Sonicators/UltrasonicSystem/Hardware/45mm/ParabolicHorn/ReactionChamber/Front.dxf

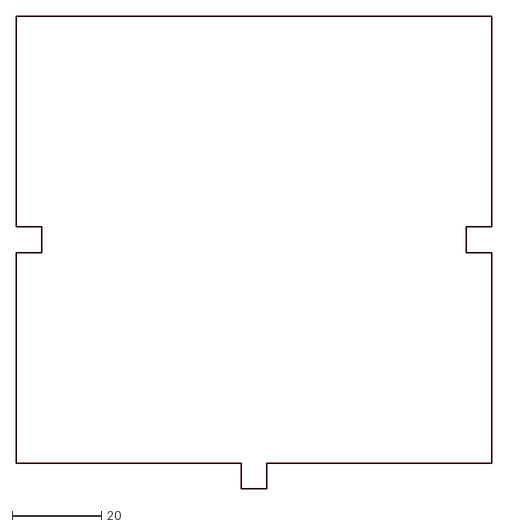
[picture p15: CAD file, 2015-09-21]
Hardware/45mm/ParabolicHorn/ReactionChamber/Front.dxf
106.4 x 105.7
