Sonicators/UltrasonicSystem/Hardware/45mm/StepHorn/DrillPressMount/UpperClamp.dxf

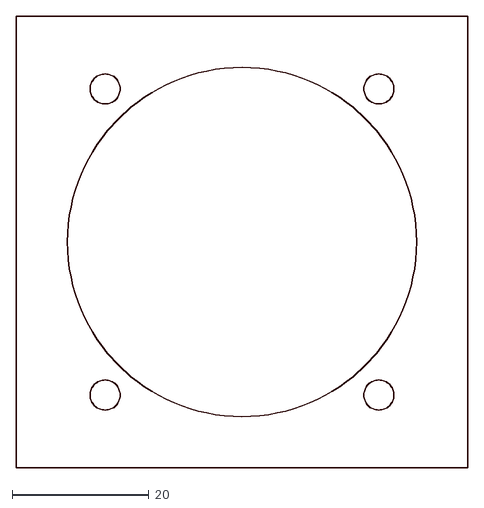
[picture p16: CAD file, 2015-09-21]
Hardware/45mm/StepHorn/DrillPressMount/UpperClamp.dxf
66.0 x 66.0
