Sonicators/UltrasonicSystem/Hardware/67mm/CameraMount/Ring.dxf

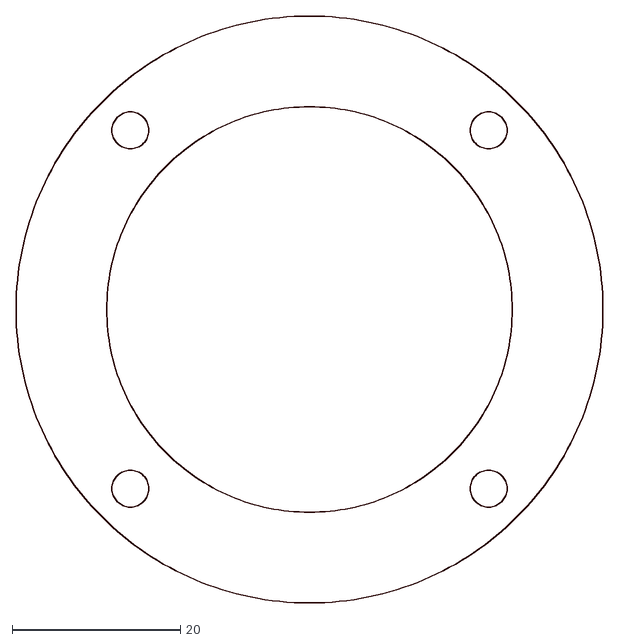
[picture p17: CAD file, 2015-09-21]
Hardware/67mm/CameraMount/Ring.dxf
69.8 x 69.8
