Sonicators/UltrasonicSystem/Hardware/67mm/Clamp/UpperClamp.dxf

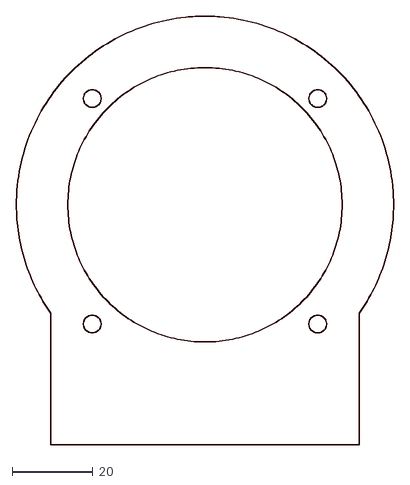
[picture p18: CAD file, 2015-09-21]
Hardware/67mm/Clamp/UpperClamp.dxf
93.6 x 106.4
