Sonicators/UltrasonicSystem/Hardware/45mm/CameraMount/LowerClamp.dxf

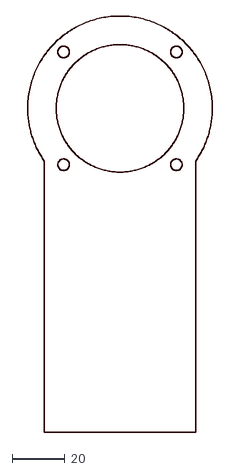
[picture p19: CAD file, 2015-09-21]
Hardware/45mm/CameraMount/LowerClamp.dxf
69.8 x 157.4
