Sonicators/UltrasonicSystem/Hardware/45mm/Clamp/LowerClamp.dxf

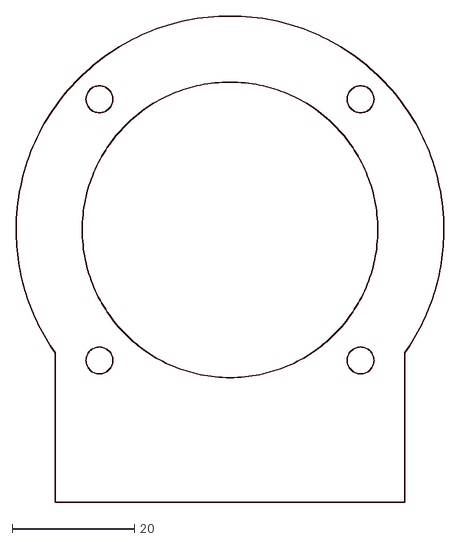
[picture p20: CAD file, 2015-09-21]
Hardware/45mm/Clamp/LowerClamp.dxf
69.8 x 79.4
