Sonicators/UltrasonicSystem/Hardware/45mm/DrillPressMount/UpperClamp.dxf

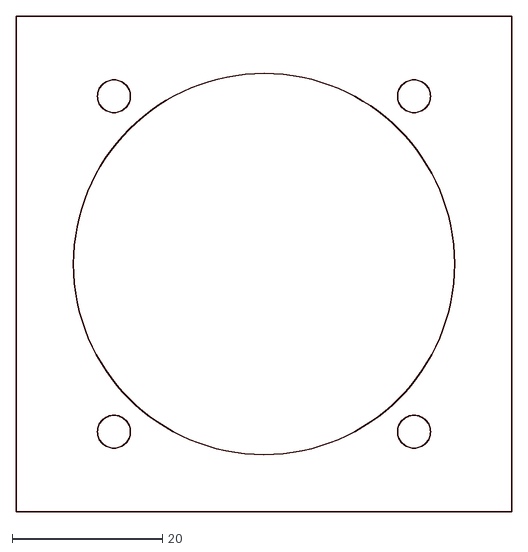
[picture p21: CAD file, 2015-09-21]
Hardware/45mm/DrillPressMount/UpperClamp.dxf
66.0 x 66.0
