Sonicators/UltrasonicSystem/Hardware/45mm/ParabolicHorn/ReactionChamber/Gasket.dxf

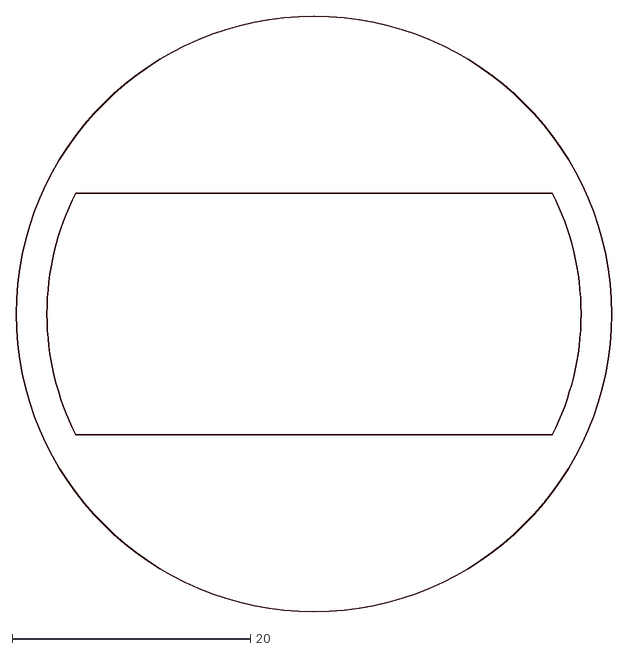
[picture p22: CAD file, 2015-09-21]
Hardware/45mm/ParabolicHorn/ReactionChamber/Gasket.dxf
50.0 x 50.0
