Sonicators/UltrasonicSystem/Hardware/67mm/CameraMount/UpperClamp.dxf

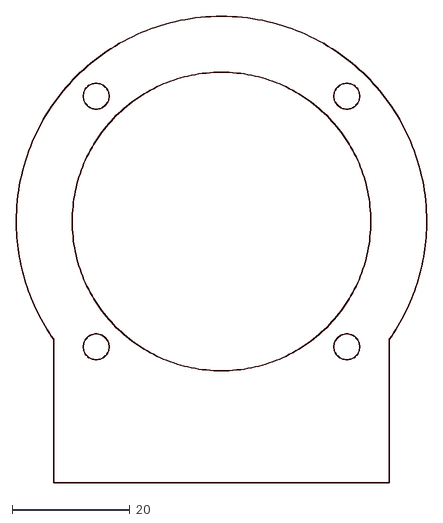
[picture p23: CAD file, 2015-09-21]
Hardware/67mm/CameraMount/UpperClamp.dxf
69.8 x 79.4
