Sonicators/UltrasonicSystem/Hardware/67mm/Clamp/LowerClamp.dxf

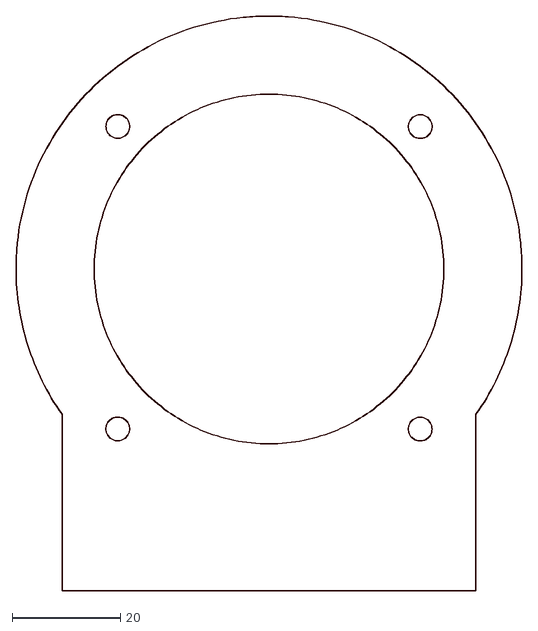
[picture p24: CAD file, 2015-09-21]
Hardware/67mm/Clamp/LowerClamp.dxf
93.6 x 106.4
