Sonicators/UltrasonicSystem/Hardware/45mm/CameraMount/Ring.dxf

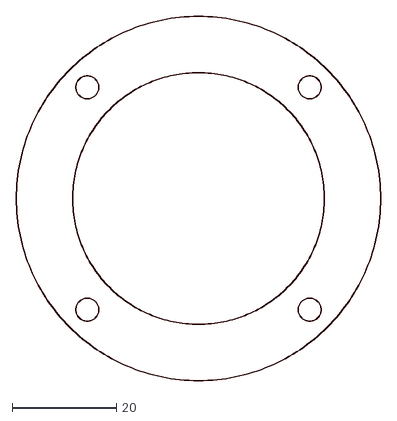
[picture p25: CAD file, 2015-09-21]
Hardware/45mm/CameraMount/Ring.dxf
69.8 x 69.8
