Sonicators/UltrasonicSystem/Hardware/45mm/ParabolicHorn/DrillPressMount/Gasket.dxf

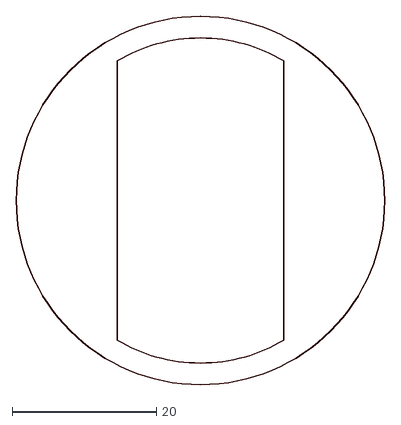
[picture p26: CAD file, 2015-09-21]
Hardware/45mm/ParabolicHorn/DrillPressMount/Gasket.dxf
51.0 x 51.0
