Sonicators/UltrasonicSystem/Hardware/45mm/ParabolicHorn/ReactionChamber/TubeHolder.dxf

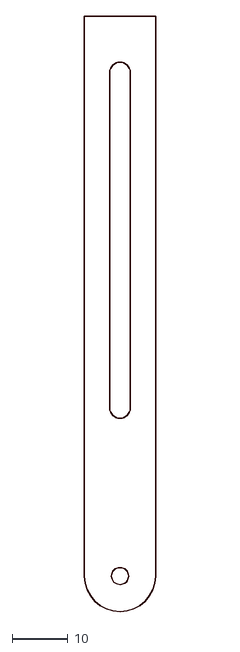
[picture p27: CAD file, 2015-09-21]
Hardware/45mm/ParabolicHorn/ReactionChamber/TubeHolder.dxf
12.7 x 106.3
