Sonicators/UltrasonicSystem/Hardware/67mm/CameraMount/BraceCorners.dxf

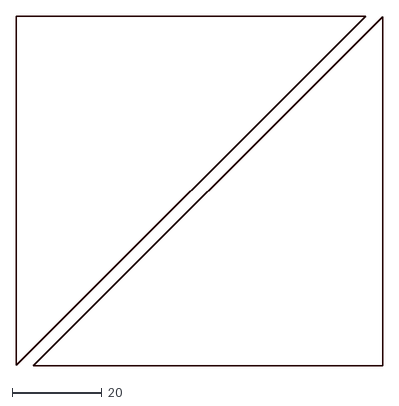
[picture p28: CAD file, 2015-09-21]
Hardware/67mm/CameraMount/BraceCorners.dxf
81.8 x 78.1
