Sonicators/UltrasonicSystem/Hardware/45mm/CameraMount/CameraBase.dxf

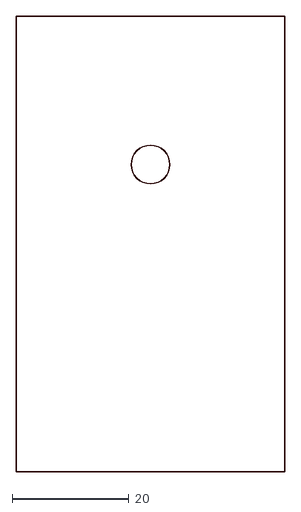
[picture p29: CAD file, 2015-09-21]
Hardware/45mm/CameraMount/CameraBase.dxf
46.0 x 78.0
