Sonicators/UltrasonicSystem/Hardware/45mm/ParabolicHorn/ReactionChamber/Side.dxf

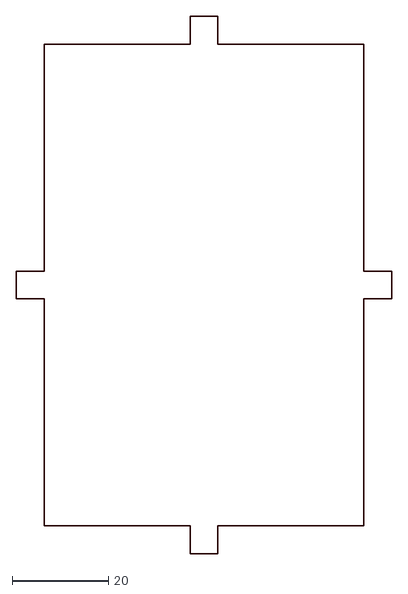
[picture p30: CAD file, 2015-09-21]
Hardware/45mm/ParabolicHorn/ReactionChamber/Side.dxf
77.8 x 111.5
