Sonicators/UltrasonicSystem/Hardware/67mm/CameraMount/Gasket.dxf

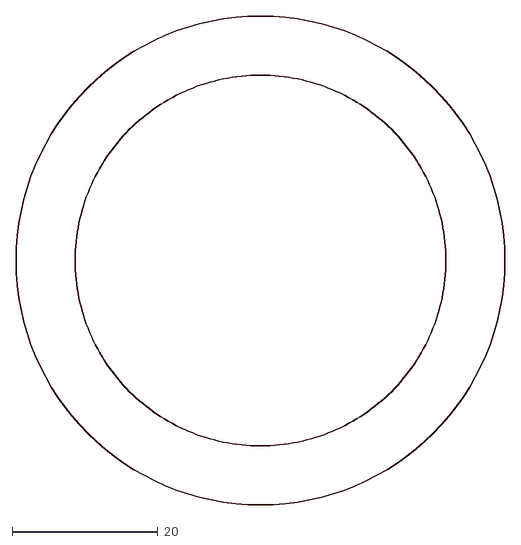
[picture p31: CAD file, 2015-09-21]
Hardware/67mm/CameraMount/Gasket.dxf
67.0 x 67.0
