Sonicators/UltrasonicSystem/Hardware/45mm/ParabolicHorn/ReactionChamber/TopRoundGasket.dxf

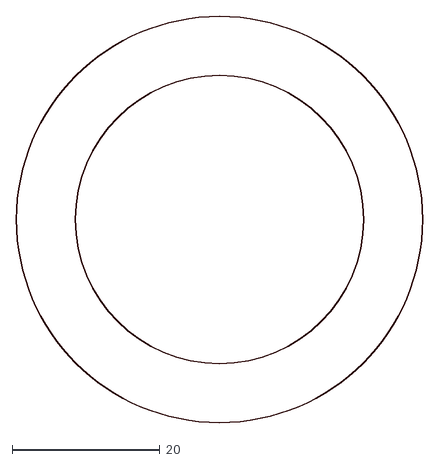
[picture p32: CAD file, 2015-09-21]
Hardware/45mm/ParabolicHorn/ReactionChamber/TopRoundGasket.dxf
55.0 x 55.0
