Sonicators/UltrasonicSystem/Hardware/67mm/CameraMount/LowerClamp.dxf

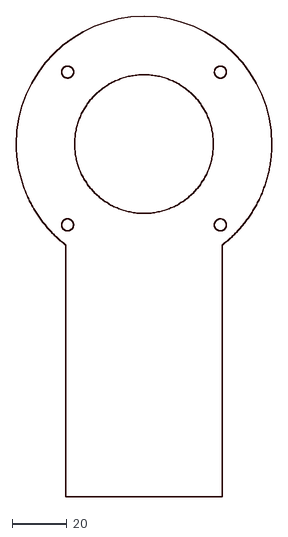
[picture p33: CAD file, 2015-09-21]
Hardware/67mm/CameraMount/LowerClamp.dxf
93.6 x 176.0
