Sonicators/UltrasonicSystem/Hardware/45mm/ParabolicHorn/ReactionChamber/TopRoundWide.dxf

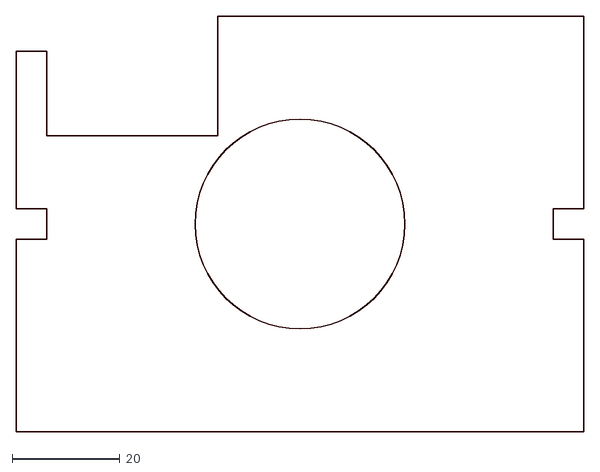
[picture p34: CAD file, 2015-09-21]
Hardware/45mm/ParabolicHorn/ReactionChamber/TopRoundWide.dxf
105.6 x 77.3
