Sonicators/UltrasonicSystem/Hardware/45mm/ParabolicHorn/ReactionChamber/Base.dxf

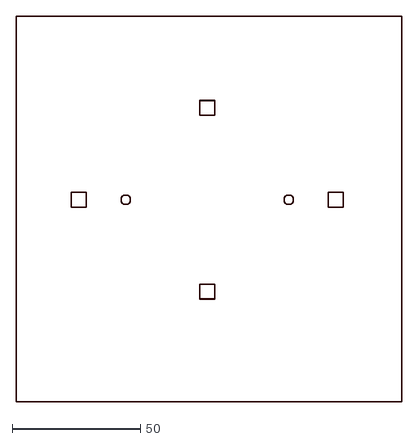
[picture p35: CAD file, 2015-09-21]
Hardware/45mm/ParabolicHorn/ReactionChamber/Base.dxf
150.0 x 150.0
