Sonicators/UltrasonicSystem/Hardware/45mm/ParabolicHorn/ReactionChamber/Back.dxf

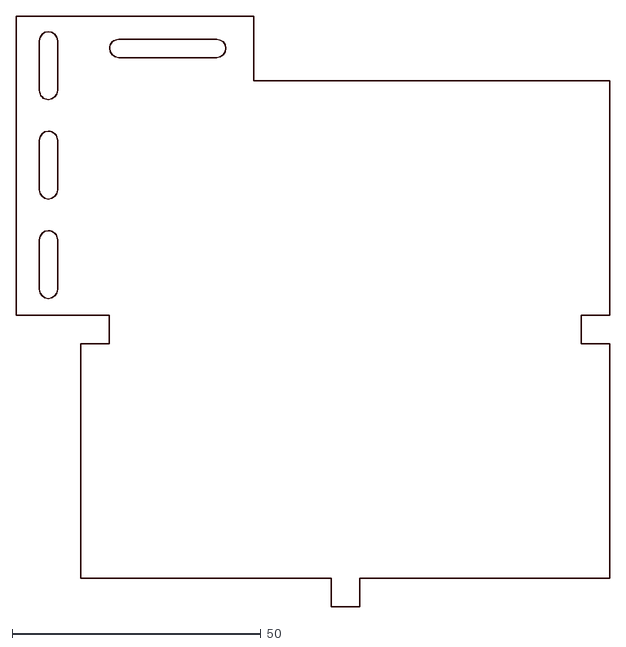
[picture p36: CAD file, 2015-09-21]
Hardware/45mm/ParabolicHorn/ReactionChamber/Back.dxf
119.4 x 118.8
