Sonicators/UltrasonicSystem/Hardware/45mm/ParabolicHorn/ReactionChamber/HolderNut.dxf

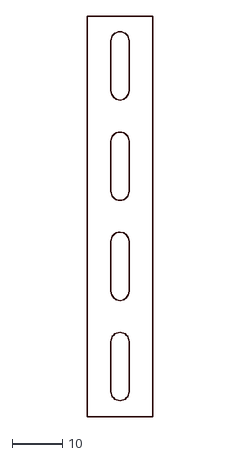
[picture p37: CAD file, 2015-09-21]
Hardware/45mm/ParabolicHorn/ReactionChamber/HolderNut.dxf
13.0 x 80.0
