Sonicators/UltrasonicSystem/Software/Sone/Src/AD9833.c

//////////////////////////////////////////////////////////////////////////////////////////
//////////////////////////////////////////////////////////////////////////////////////////
//
//      Copyright (C) 2015 Peter Walsh, Milford, NH 03055
//      All Rights Reserved
//
//  FILE
//      AD9833.c
//
//  SYNOPSIS
//
//  DESCRIPTION
//
//      Simple AD9833 interface
//
//////////////////////////////////////////////////////////////////////////////////////////
//
//  MIT LICENSE
//
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
//////////////////////////////////////////////////////////////////////////////////////////
//////////////////////////////////////////////////////////////////////////////////////////

#include <avr/io.h>
#include <string.h>

#include "PortMacros.h"
#include "AD9833.h"
#include "SPIInline.h"

//////////////////////////////////////////////////////////////////////////////////////////
//////////////////////////////////////////////////////////////////////////////////////////
//
// Data declarations
//
//////////////////////////////////////////////////////////////////////////////////////////
//////////////////////////////////////////////////////////////////////////////////////////

static struct {
    uint16_t    Freq;               // Currently set frequency

    bool        IsOn;               // TRUE if output is currently on

    } AD9833 NOINIT;

//
// See the datasheet for description
//
#define FREQ0       0b0100000000000000      // Frequency register 0
#define FREQ1       0b1000000000000000      // Frequency register 1

#define PHASE0      0b11000000      // Phase     register 0
#define PHASE1      0b11100000      // Phase     register 1

#define UNUSED15    0b10000000      // ...unused
#define UNUSED14    0b01000000      // ...unused
#define B28         0b00100000      // Use full 28-bit registers
#define HLB         0b00010000
#define FSELECT     0b00001000      // Select frequency register
#define PSELECT     0b00000100      // Select phase register
#define UNUSED9     0b00000010      // ...unused
#define RESET       0b00000001      // Reset registers to zero, output is midscale

#define SLEEP       0b10000000
#define SLEEP12     0b01000000
#define OPBITEN     0b00100000
#define UNUSED4     0b00010000      // ...unused
#define DIV2        0b00001000
#define UNUSED2     0b00000100      // ...unused
#define MODE        0b00000010
#define UNUSED0     0b00000001      // ...unused

#define SEND_2BYTES(_x_,_y_) {                                                              \
    _CLR_BIT(_PORT(AD9833_FSYNC_PORT),AD9833_FSYNC_PIN);/* Clr FSYNC for data */            \
    PutSPIByte(_x_);                                    /* Send 1st byte      */            \
    PutSPIByte(_y_);                                    /* Send 2nd byte      */            \
    _SET_BIT(_PORT(AD9833_FSYNC_PORT),AD9833_FSYNC_PIN);/* Set to strobe data */            \
    }                                                                                       \


//////////////////////////////////////////////////////////////////////////////////////////
//////////////////////////////////////////////////////////////////////////////////////////
//
// AD9833Init - Initialize AD9833 system
//
// Inputs:      None.
//
// Outputs:     None.
//
void AD9833Init(void) {

    memset(&AD9833,0,sizeof(AD9833));


    //////////////////////////////////////////////////////////////////////////////////////
    //
    // Initialize the control outputs
    //
    _SET_BIT( _DDR(AD9833_FSYNC_PORT),AD9833_FSYNC_PIN);    // FSYNC is an output
    _SET_BIT(_PORT(AD9833_FSYNC_PORT),AD9833_FSYNC_PIN);    // Set high  for now

    AD9833Output(AD9833_OFF,0);
    }

//////////////////////////////////////////////////////////////////////////////////////////
//////////////////////////////////////////////////////////////////////////////////////////
//
// AD9833Output - Set mode and frequency
//
// Inputs:      Mode        AD9833_MODE of output (ie - AD9833_SIN, AD9833_SQ, etc.)
//              Frequency   of output
//
// Outputs:     None.
//
// NOTE: If Mode = AD9833_OFF, frequency is ignored (pass 0, for example).
//
void AD9833Output(AD9833_MODE Mode,uint16_t Freq) {

    //////////////////////////////////////////////////////////////////////////////////////
    //
    // The 9833 chip uses an unusual CPOL/CPHA combination. Since it's unusual, we
    //   encapsulate it here, rather than complicate the SPIInline module.
    //
    uint8_t SavedSPCR = SPCR;
    _SET_BIT(SPCR,CPOL);
    _CLR_BIT(SPCR,CPHA);

    SEND_2BYTES(B28 | RESET,0);                     // Use 28-bit regs, reset

    if( Mode == AD9833_OFF ) {
        SPCR        = SavedSPCR;
        AD9833.IsOn = false;;
        return;
        }

    AD9833.Freq = Freq;
    AD9833.IsOn = true;

    //////////////////////////////////////////////////////////////////////////////////////
    //
    // Calculate the clock divisor, per the AD9833 datasheet:
    //
    //   Freq    = (Divisor*CLKIN)/(2^28)
    //   Divisor = Freq*(2^28)/CLKIN
    //
    // CLKIN in our application is 25,000,000
    //
    // (2^28)/CLKIN = (2^22)/(5^8)      (Factor out 2^6 in both numbers)
    //
    // The shift/div below works for frequencies to 65535 without
    //   overflowing 32-bit arithmetic.
    //
    union {
        uint32_t    Long;           // Clock divisor, sent to chip
        uint16_t    Words[2];       // Referenced as words
        uint8_t     Bytes[4];       // Referenced as bytes
        } Div;


    Div.Long = Freq;
    Div.Long = (Div.Long << 14)/625;
    Div.Long = (Div.Long <<  8)/625;

    //////////////////////////////////////////////////////////////////////////////////////
    //
    // Calculate the frequency register highword and lowword
    //
    // Note: I normally avoid unions, but the generated code for shift/mask the Div
    //         value is excessive. The compiler isn't smart enough to optimize bite-wise
    //         shifts, so I do it here with a union.
    //
    union {
        uint16_t    Word;
        uint8_t     Bytes[2];
        } FreqLow;                  // Low  order 14 bits of freq
    union {
        uint16_t    Word;
        uint8_t     Bytes[2];
        } FreqHigh;                 // High order 14 bits of freq

    FreqLow .Word = FREQ0 | (Div.Words[0] & 0x3FFF);
    FreqHigh.Word = FREQ0 | (Div.Words[1] << 2) | (Div.Bytes[1] >> 6);

    //////////////////////////////////////////////////////////////////////////////////////
    //
    // Send the data to the chip
    //
    SEND_2BYTES(FreqLow .Bytes[1],FreqLow .Bytes[0]);   // Low  14 bits frequency
    SEND_2BYTES(FreqHigh.Bytes[1],FreqHigh.Bytes[0]);   // High 14-bits frequency
    SEND_2BYTES(PHASE0,0);                              // Set phase to zero

    if     ( Mode == AD9833_SIN ) { SEND_2BYTES(B28      ,0); }
    else if( Mode == AD9833_SQ  ) { SEND_2BYTES(B28,OPBITEN | DIV2); }
    else if( Mode == AD9833_TRI ) { SEND_2BYTES(B28,   MODE); }

    SPCR = SavedSPCR;
    }

//////////////////////////////////////////////////////////////////////////////////////////
//////////////////////////////////////////////////////////////////////////////////////////
//
// AD9833IsOn - Return whether output is on
//
// Inputs:      None.
//
// Outputs:     TRUE  if output enabled
//              FALSE otherwise
//
bool AD9833IsOn(void) { return AD9833.IsOn; }


//////////////////////////////////////////////////////////////////////////////////////////
//////////////////////////////////////////////////////////////////////////////////////////
//
// AD9833GetFreq - Return current frequency
//
// Inputs:      None
//
// Outputs:     Currently set frequency
//
uint16_t AD9833GetFreq(void) { return AD9833.Freq; }
